jinsu1011/safenest-embedded-competition-bridege/final-report/assets/hw_esp32_wiring.jpg

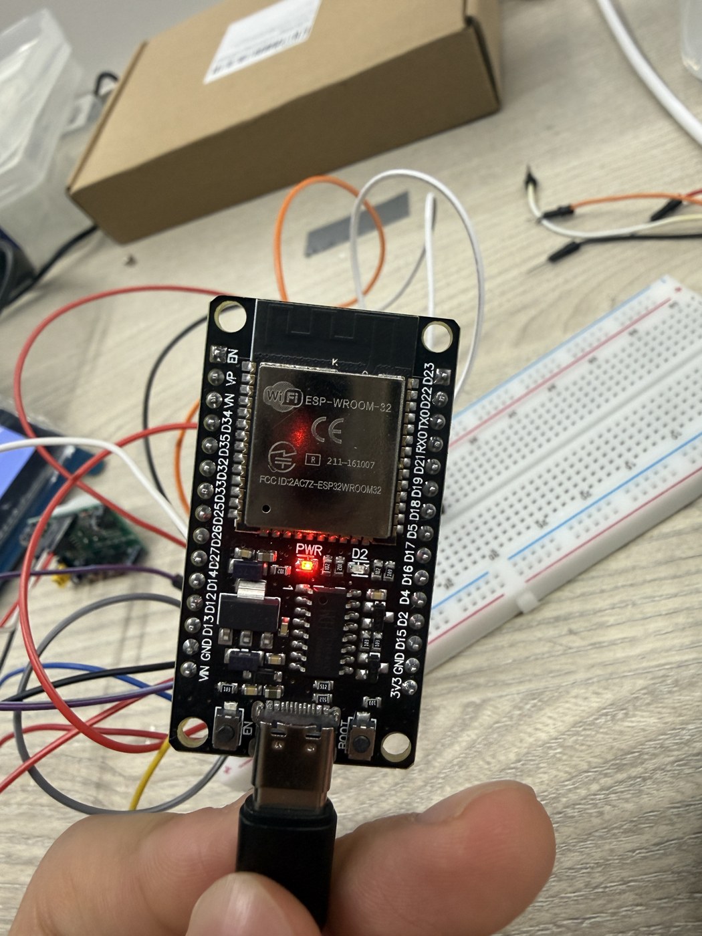
final-report/assets/hw_esp32_wiring.jpg
