jinsu1011/safenest-embedded-competition-bridege/RaspberryPi/Runtime/backend/runtime_status.py

"""Derived roadmap-0.8.6 runtime capability status for existing API responses.

This module deliberately stores nothing. It projects the existing latest sensor
state and AI result documents into stable, machine-readable capability fields.
It does not select models, invoke inference, or change risk behavior.
"""

from __future__ import annotations

from typing import Any, Mapping

from paths import MODEL_MANIFEST
from thermal_test_selector import (
    ThermalSelectorError,
    describe_thermal_selection,
    load_model_manifest,
    peek_configured_thermal_selector,
)


SENSOR_IDS = ("mmwave", "thermal", "co2", "pir")
_THERMAL_MANIFEST: Mapping[str, Any] | None = None
_THERMAL_MANIFEST_LOADED = False


def runtime_status_document(
    state: Mapping[str, Any],
    ai_results: Mapping[str, Any],
) -> dict[str, Any]:
    """Return a non-persistent capability projection for the current publication."""

    sensors = _mapping(state.get("sensors"))
    projected = {
        "co2": _co2_status(_mapping(sensors.get("co2")), _mapping(ai_results.get("co2"))),
        "thermal": _thermal_status(
            _mapping(sensors.get("thermal")), _mapping(ai_results.get("thermal"))
        ),
        "mmwave": _mmwave_status(
            _mapping(sensors.get("mmwave")), _mapping(ai_results.get("mmwave"))
        ),
        "pir": _pir_status(_mapping(sensors.get("pir"))),
    }
    global_status = _global_status(projected)
    return {
        "status": global_status,
        "sensors": projected,
        "limitations": [
            sensor_id
            for sensor_id, entry in projected.items()
            if entry["ai_status"] in {"BLOCKED", "MODEL_PENDING", "UNAVAILABLE"}
        ],
    }


def _co2_status(sensor: Mapping[str, Any], result: Mapping[str, Any]) -> dict[str, Any]:
    status = _sensor_base(sensor)
    status["artifact_status"] = "PRESENT"
    if status["sensor_status"] != "AVAILABLE":
        return _blocked_for_sensor(status)

    if bool(result.get("available")):
        status.update(
            {
                "input_contract_status": "SATISFIED",
                "ai_status": "ACTIVE",
                "blocked_reason": None,
                "output_status": "AVAILABLE",
            }
        )
        return status

    error = str(result.get("error") or "")
    if error == "INPUT_UNAVAILABLE":
        status.update(
            {
                "input_contract_status": "UNSATISFIED",
                "ai_status": "BLOCKED",
                "blocked_reason": "INPUT_CONTRACT_UNSATISFIED",
                "output_status": "NOT_AVAILABLE",
            }
        )
    elif error == "WINDOW_WARMING_UP":
        status.update(
            {
                "input_contract_status": "WARMING_UP",
                "ai_status": "BLOCKED",
                "blocked_reason": "INPUT_WARMUP",
                "output_status": "NOT_AVAILABLE",
            }
        )
    else:
        status.update(
            {
                "input_contract_status": "UNKNOWN",
                "ai_status": "UNAVAILABLE",
                "blocked_reason": error or "MODEL_RUNTIME_UNAVAILABLE",
                "output_status": "NOT_AVAILABLE",
            }
        )
    return status


def _thermal_manifest() -> Mapping[str, Any]:
    global _THERMAL_MANIFEST, _THERMAL_MANIFEST_LOADED
    if _THERMAL_MANIFEST_LOADED:
        return _THERMAL_MANIFEST or {}
    _THERMAL_MANIFEST_LOADED = True
    try:
        _THERMAL_MANIFEST = load_model_manifest(MODEL_MANIFEST)
    except (OSError, ValueError, ThermalSelectorError):
        _THERMAL_MANIFEST = {}
    return _THERMAL_MANIFEST


def _thermal_identity(metadata: Mapping[str, Any]) -> dict[str, Any]:
    """Process-selected Thermal identity, even before a valid prediction."""

    selector = str(
        metadata.get("model_selector") or peek_configured_thermal_selector() or ""
    ).strip()
    described: Mapping[str, Any] = {}
    if selector:
        described = describe_thermal_selection(selector, _thermal_manifest())
    sha = (
        metadata.get("model_sha256")
        or metadata.get("sha256")
        or described.get("sha256")
    )
    return {
        "model_selector": selector,
        "model_id": metadata.get("model_id") or described.get("model_id"),
        "model_sha256": sha,
        "preprocessing_id": metadata.get("preprocessing_id")
        or described.get("preprocessing_id"),
    }


def _thermal_status(sensor: Mapping[str, Any], result: Mapping[str, Any]) -> dict[str, Any]:
    status = _sensor_base(sensor)
    # The public-SDT FP32 model is the active inference/risk selector. Its
    # HUMAN_FALL_PROXY output contributes bounded risk but has no emergency
    # authority until Pi and real-fall validation are complete.
    status["artifact_status"] = "PRESENT"
    metadata = _mapping(result.get("metadata"))
    status.update(_thermal_identity(metadata))
    status["safety_status"] = "LIMITED_PROXY_NO_EMERGENCY"
    if status["sensor_status"] != "AVAILABLE":
        return _blocked_for_sensor(status)
    if bool(result.get("available")):
        status.update(
            {
                "input_contract_status": "SATISFIED_WITH_LIMITATIONS",
                "ai_status": "ACTIVE",
                "blocked_reason": None,
                "output_status": "AVAILABLE",
                "risk_authority": metadata.get(
                    "risk_authority", "LIMITED_POSTURE_PROXY"
                ),
            }
        )
        status.update(_thermal_identity(metadata))
        return status
    error = str(result.get("error") or "")
    status.update(
        {
            "input_contract_status": "VALIDATED_WITH_LIMITATIONS",
            "ai_status": "BLOCKED",
            "blocked_reason": error or "THERMAL_MODEL_RUNTIME_UNAVAILABLE",
            "output_status": "NOT_AVAILABLE",
        }
    )
    return status


def _mmwave_status(sensor: Mapping[str, Any], result: Mapping[str, Any]) -> dict[str, Any]:
    status = _sensor_base(sensor)
    status["artifact_status"] = "PRESENT"
    if status["sensor_status"] != "AVAILABLE":
        return _blocked_for_sensor(status)

    if bool(result.get("available")):
        status.update(
            {
                "input_contract_status": "SATISFIED",
                "ai_status": "ACTIVE",
                "blocked_reason": None,
                "output_status": "AVAILABLE",
            }
        )
        return status

    error = str(result.get("error") or "")
    metadata = result.get("metadata") if isinstance(result.get("metadata"), Mapping) else {}
    window_status = str(metadata.get("canonical_window_status") or "")
    if error == "CANONICAL_FRESHNESS_METADATA_MISSING" or window_status == "WINDOW_UNAVAILABLE":
        contract, reason = "UNSATISFIED", error or "CANONICAL_FRESHNESS_METADATA_MISSING"
    elif error == "INSUFFICIENT_CONTINUOUS_DURATION" or window_status == "RESPIRATORY_WINDOW_WARMING_UP":
        contract, reason = "WARMING_UP", error or "INPUT_WARMUP"
    elif error == "PRESENCE_STATE_UNAVAILABLE":
        contract, reason = "UNSATISFIED", error
    elif error == "NO_VALID_PERSON":
        contract, reason = "SATISFIED", error
    elif error:
        contract, reason = "UNKNOWN", error
    else:
        values = _mapping(sensor.get("values"))
        if not _finite_trio(values, ("breath_phase", "ts_monotonic_ms", "phase_age_ms")):
            contract, reason = "UNSATISFIED", "CANONICAL_FRESHNESS_METADATA_MISSING"
        elif values.get("presence_available") is not True:
            contract, reason = "UNSATISFIED", "PRESENCE_STATE_UNAVAILABLE"
        else:
            contract, reason = "UNKNOWN", "MODEL_RUNTIME_UNAVAILABLE"
    status.update(
        {
            "input_contract_status": contract,
            "ai_status": "BLOCKED",
            "blocked_reason": reason,
            "output_status": "NOT_AVAILABLE",
        }
    )
    return status


def _pir_status(sensor: Mapping[str, Any]) -> dict[str, Any]:
    status = _sensor_base(sensor)
    motion = bool(_mapping(sensor.get("values")).get("motion"))
    status.update(
        {
            "artifact_status": "NOT_APPLICABLE",
            "input_contract_status": "NOT_APPLICABLE",
            "ai_status": "NOT_APPLICABLE",
            "blocked_reason": None,
            "output_status": "NOT_APPLICABLE",
            "sensor_value_status": "MOTION" if motion else "NO_MOTION",
        }
    )
    return status


def _sensor_base(sensor: Mapping[str, Any]) -> dict[str, Any]:
    raw_status = str(sensor.get("status") or "NO_DATA")
    sensor_status = {
        "LIVE": "AVAILABLE",
        "STALE": "STALE",
        "INVALID": "INVALID",
    }.get(raw_status, "UNAVAILABLE")
    connectivity = (
        "DISCONNECTED"
        if raw_status == "DISCONNECTED"
        else "CONNECTED"
        if raw_status in {"LIVE", "STALE", "INVALID"} or bool(sensor.get("connected"))
        else "UNKNOWN"
    )
    freshness = {
        "LIVE": "CURRENT",
        "STALE": "STALE",
        "INVALID": "INVALID",
        "DISCONNECTED": "STALE" if bool(sensor.get("stale")) else "UNKNOWN",
    }.get(raw_status, "UNKNOWN")
    return {
        "sensor_status": sensor_status,
        "sensor_connectivity": connectivity,
        "data_freshness": freshness,
        "artifact_status": "UNKNOWN",
        "input_contract_status": "NOT_EVALUATED",
        "ai_status": "NOT_EVALUATED",
        "blocked_reason": None,
        "output_status": "NOT_AVAILABLE",
    }


def _blocked_for_sensor(status: dict[str, Any]) -> dict[str, Any]:
    reason = {
        "STALE": "SENSOR_STALE",
        "INVALID": "SENSOR_INVALID",
        "UNAVAILABLE": "SENSOR_UNAVAILABLE",
    }.get(status["sensor_status"], "SENSOR_UNAVAILABLE")
    status.update(
        {
            "input_contract_status": "NOT_EVALUATED",
            "ai_status": "BLOCKED",
            "blocked_reason": reason,
            "output_status": "NOT_AVAILABLE",
        }
    )
    return status


def _global_status(projected: Mapping[str, Mapping[str, Any]]) -> str:
    sensor_states = [entry["sensor_status"] for entry in projected.values()]
    available_count = sensor_states.count("AVAILABLE")
    if available_count == 0:
        return "NOT_READY"
    if any(value != "AVAILABLE" for value in sensor_states):
        return "DEGRADED"
    if any(
        entry["ai_status"] in {"BLOCKED", "MODEL_PENDING", "UNAVAILABLE"}
        for entry in projected.values()
    ):
        return "READY_WITH_LIMITATIONS"
    return "READY"


def _mapping(value: object) -> Mapping[str, Any]:
    return value if isinstance(value, Mapping) else {}


def _finite_trio(values: Mapping[str, Any], fields: tuple[str, ...]) -> bool:
    return all(
        isinstance(values.get(name), (int, float)) and not isinstance(values.get(name), bool)
        for name in fields
    )
